schumar/ESP_BaPoTeSta/docs/board_v0.6_atmega_render.jpg

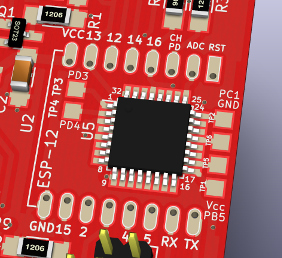
docs/board_v0.6_atmega_render.jpg
