schumar/ESP_BaPoTeSta/server/Heu_tile.jpg

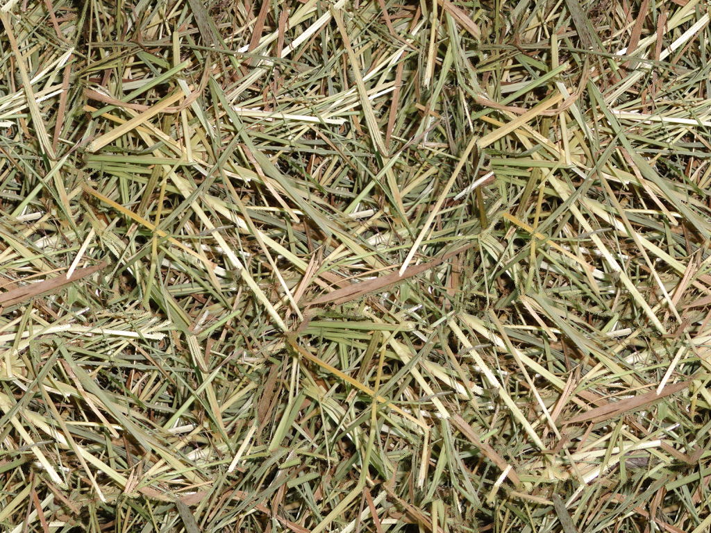
server/Heu_tile.jpg
